TilenTinta/Greenhouse_LoRa_Node/Images/PXL_20241226_143319713.jpg

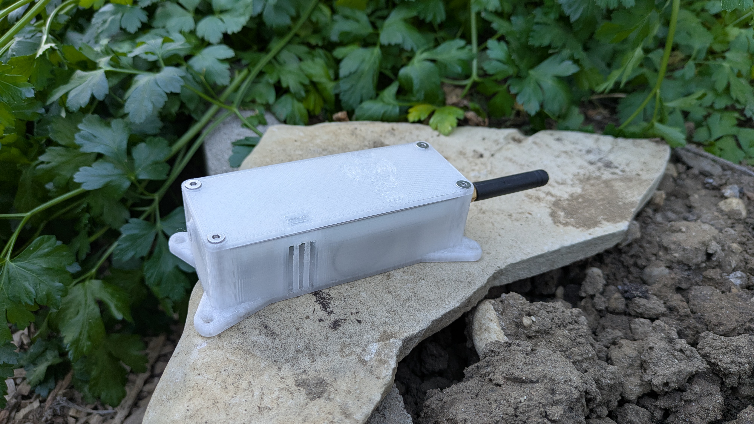
Images/PXL_20241226_143319713.jpg
