TilenTinta/Greenhouse_LoRa_Node/Images/PXL_20241226_143419090.jpg

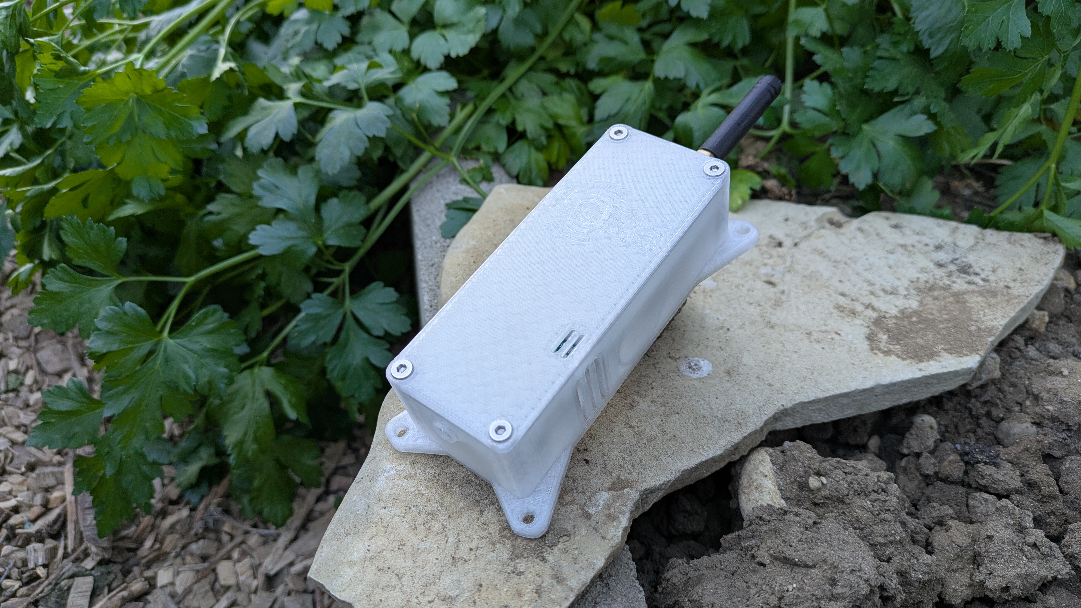
Images/PXL_20241226_143419090.jpg
