TilenTinta/Greenhouse_LoRa_Node/Images/PXL_20241226_143509718.jpg

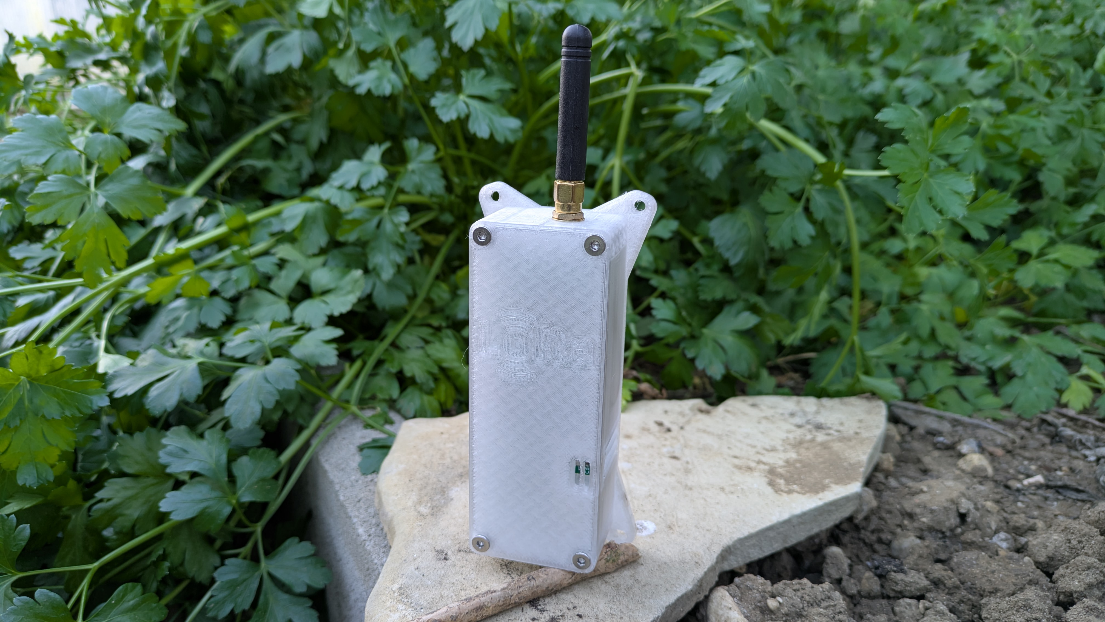
Images/PXL_20241226_143509718.jpg
