TilenTinta/Greenhouse_LoRa_Node/Images/PXL_20241226_143753341.jpg

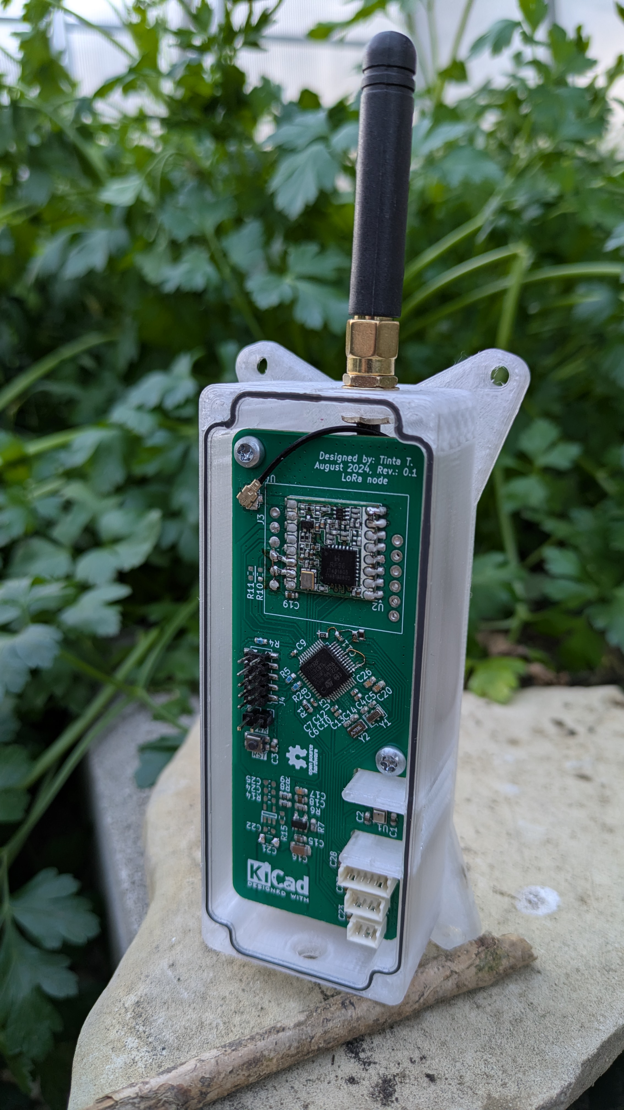
Images/PXL_20241226_143753341.jpg
