TilenTinta/Greenhouse_LoRa_Node/Images/PXL_20241226_143807855.jpg

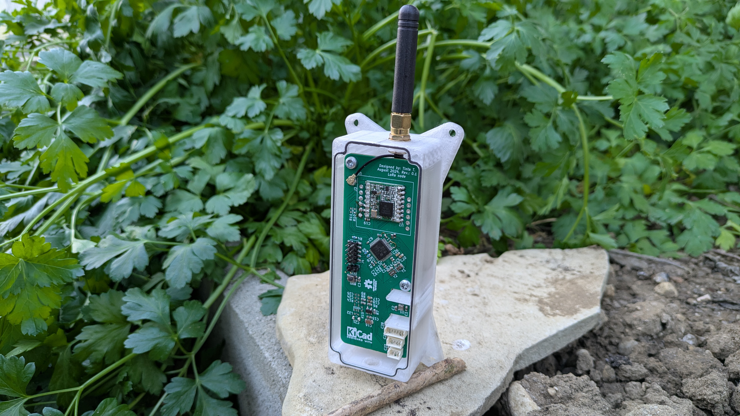
Images/PXL_20241226_143807855.jpg
