TilenTinta/Greenhouse_LoRa_Node/Images/PXL_20241226_143933485.jpg

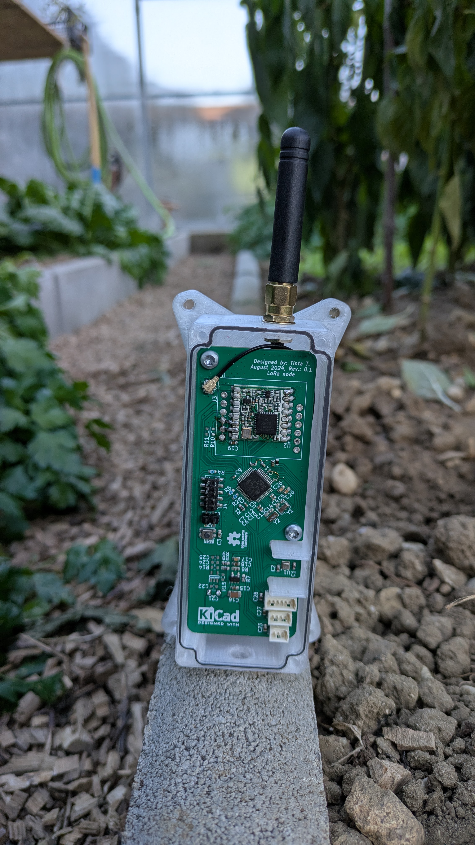
Images/PXL_20241226_143933485.jpg
