TilenTinta/Greenhouse_LoRa_Node/Images/PXL_20241226_144442999.jpg

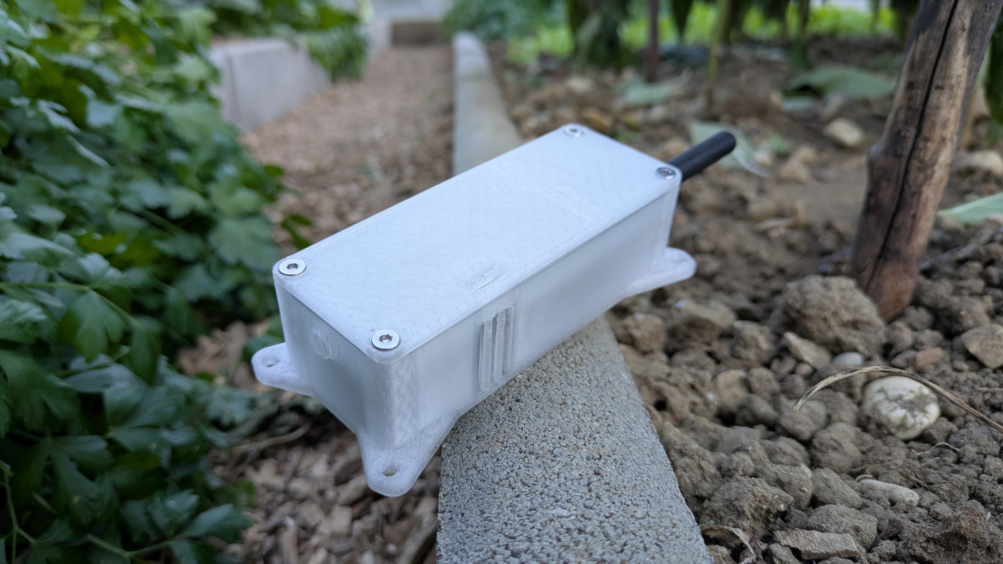
Images/PXL_20241226_144442999.jpg
