TilenTinta/Greenhouse_LoRa_Node/Images/PXL_20241226_144453190.jpg

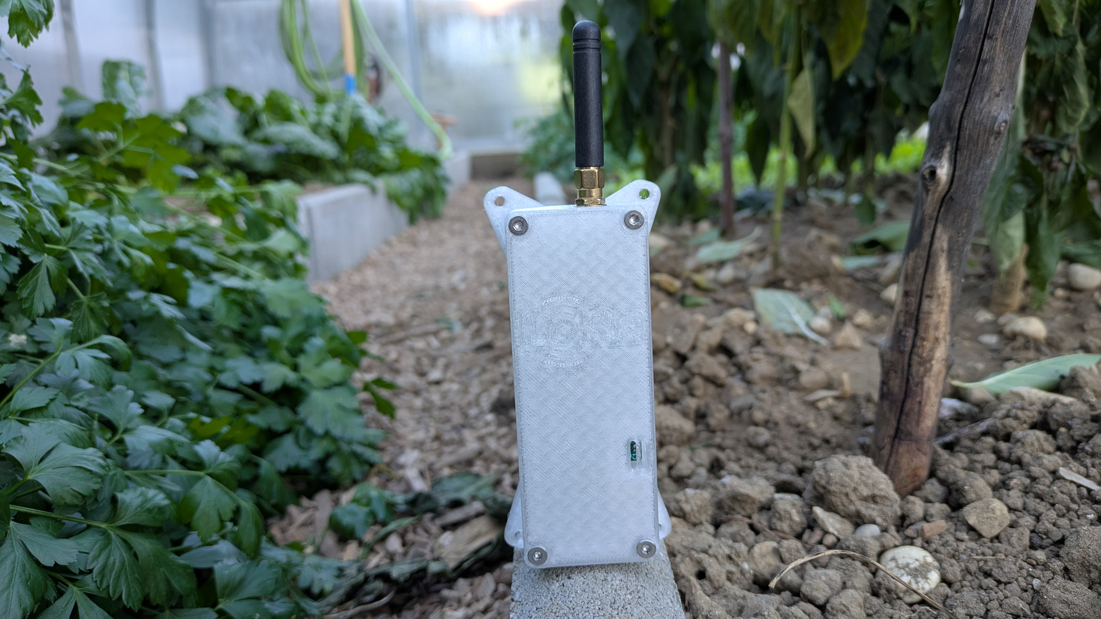
Images/PXL_20241226_144453190.jpg
