TilenTinta/Greenhouse_LoRa_Node/Images/PXL_20241226_144501793.jpg

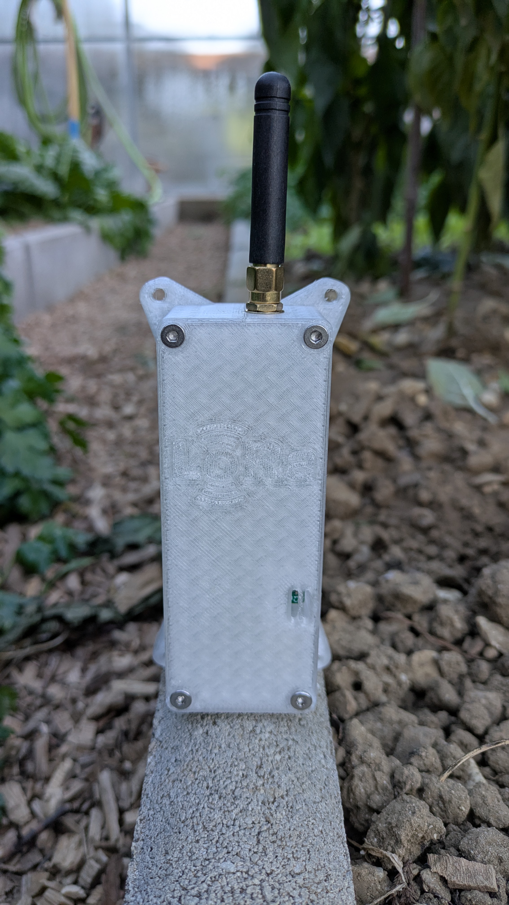
Images/PXL_20241226_144501793.jpg
