TilenTinta/Greenhouse_LoRa_Node/Firmware_L151/Core/Inc/keys.h

/*
 * keys.h
 *
 *  Created on: Nov, 2024
 *      Author: Tinta T.
 */

// !!!!! DO NOT SHARE !!!!! //
/* File contains keys used to authencticate in LoRaWAN Network */

#ifndef KEYS_H_
#define KEYS_H_

#define DEVICE_ID			1		// ID number of node

#define DEVICE_ADDRESS 		{0x26, 0x0B, 0x78, 0xE9}
#define APPSKEY 			{0xBF, 0xEC, 0xCC, 0xF7, 0x04, 0x48, 0x57, 0x71, 0x41, 0x50, 0xE2, 0xD3, 0xB2, 0x57, 0x89, 0x43}
#define NWKSKEY 			{0xE0, 0x20, 0x6E, 0x61, 0x46, 0xD2, 0x0A, 0x70, 0x9D, 0xC5, 0x1F, 0x52, 0x4C, 0x50, 0xE9, 0xCF}

#endif
